elVucko/Duino_Coin_AVR/Duino_Coin_AVR/DUINO/CH340G/Images/Duino Coin_2.jpg

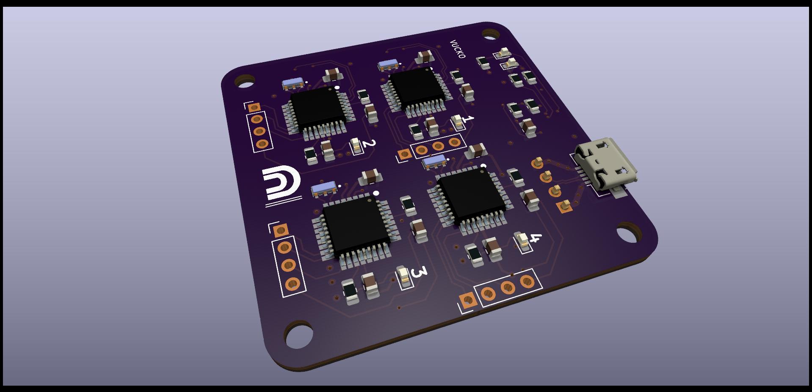
Duino_Coin_AVR/DUINO/CH340G/Images/Duino Coin_2.jpg
